HALtheWise/desnat-hopper/Final cut files/Ice chunk.SLDPRT

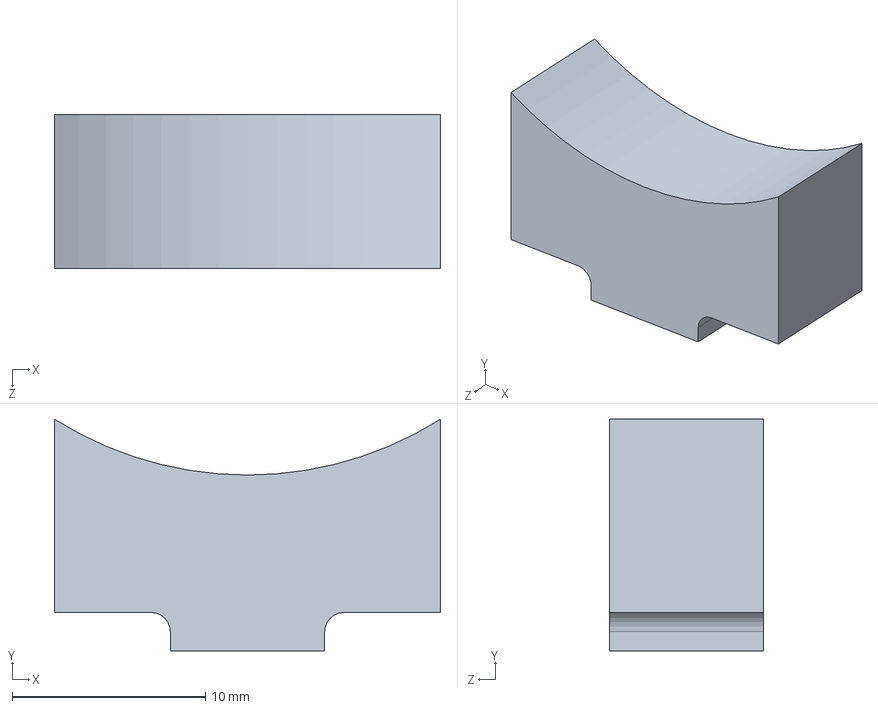
[picture p23: CAD file, 2015-10-23]
Final cut files/Ice chunk.SLDPRT
20.0 x 12.0 x 8.00 mm
