HALtheWise/desnat-hopper/H2 factory/Must be final/Cross tube holder.SLDPRT

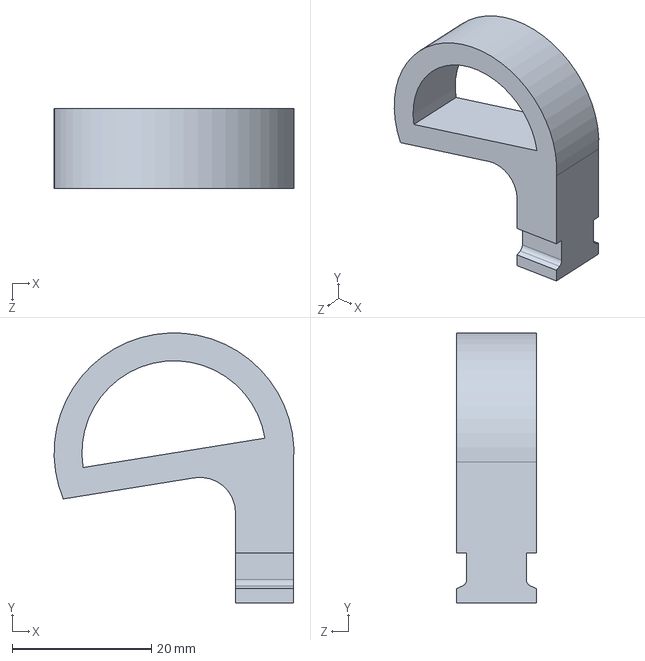
[picture p24: CAD file, 2015-10-20]
H2 factory/Must be final/Cross tube holder.SLDPRT
34.4 x 38.7 x 11.4 mm
