HALtheWise/desnat-hopper/H2 factory/Must be final/printing/Wire holder wide.STL

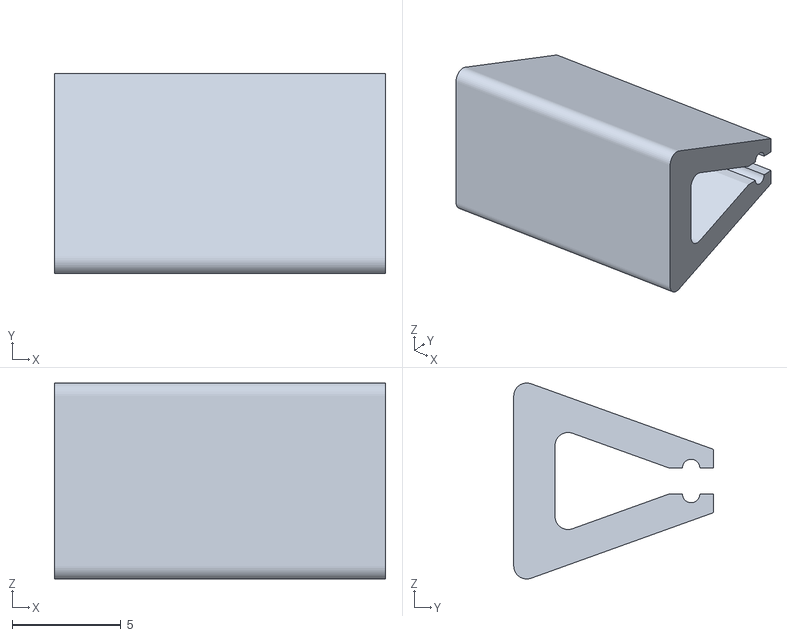
[picture p25: CAD file, 2015-10-19]
H2 factory/Must be final/printing/Wire holder wide.STL
15.2 x 9.19 x 9.02
