HALtheWise/desnat-hopper/H2 factory/Prototype 3/foot.SLDPRT

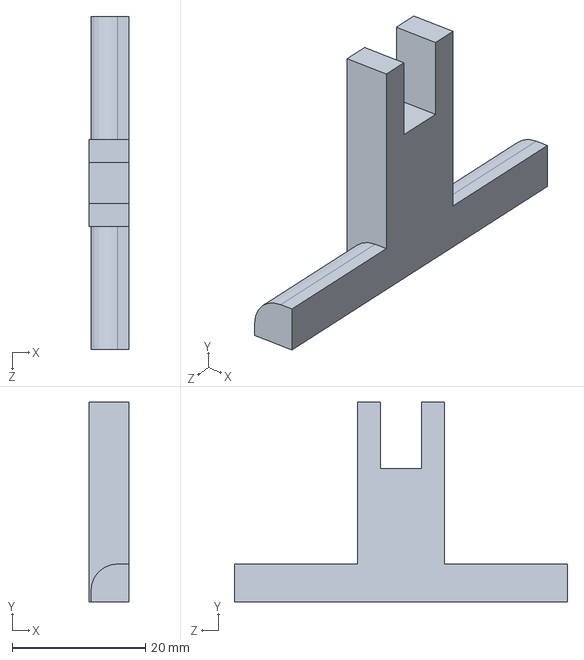
[picture p26: CAD file, 2015-10-12]
H2 factory/Prototype 3/foot.SLDPRT
6.00 x 30.0 x 50.0 mm
