HALtheWise/desnat-hopper/H2 factory/Prototype 3/print files/foot2.STL

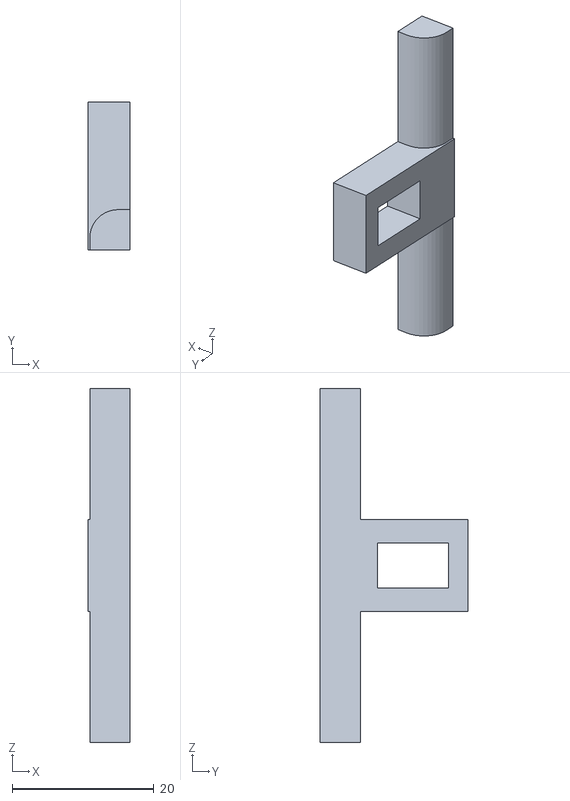
[picture p27: CAD file, 2015-10-12]
H2 factory/Prototype 3/print files/foot2.STL
6.00 x 20.9 x 50.0
