HALtheWise/desnat-hopper/H2 factory/Transport/Hose plug.SLDPRT

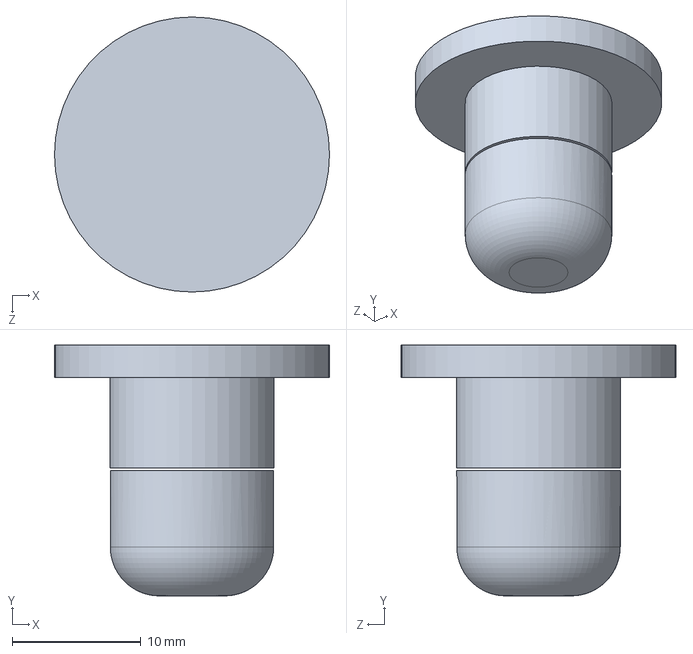
[picture p28: CAD file, 2015-10-15]
H2 factory/Transport/Hose plug.SLDPRT
21.4 x 19.5 x 21.4 mm
