HALtheWise/desnat-hopper/H2 factory/Transport/printing/Hose plug noslice.STL

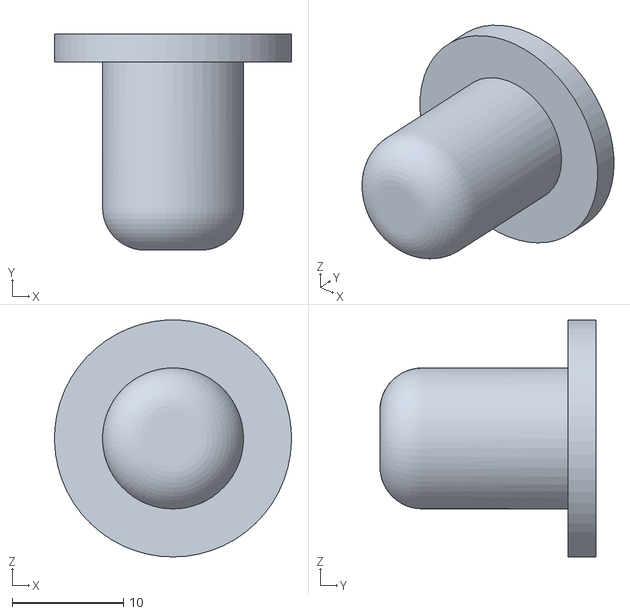
[picture p29: CAD file, 2015-10-15]
H2 factory/Transport/printing/Hose plug noslice.STL
21.4 x 19.5 x 21.3
