HALtheWise/desnat-hopper/Dynamics Simulation/Gondola.SLDPRT

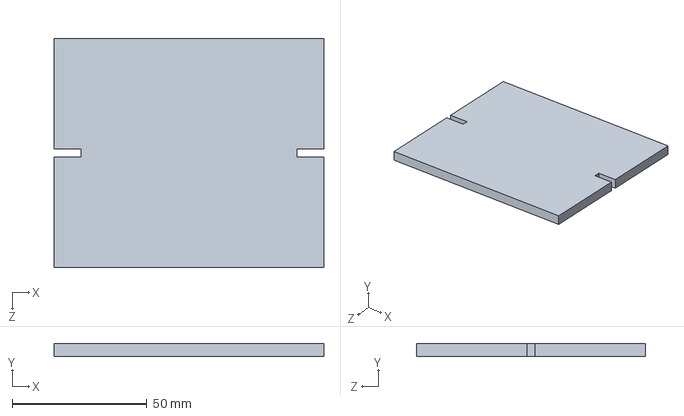
[picture p30: CAD file, 2015-10-03]
Dynamics Simulation/Gondola.SLDPRT
100.0 x 4.76 x 85.0 mm
