HALtheWise/desnat-hopper/Final cut files/Butchered solid part.SLDPRT

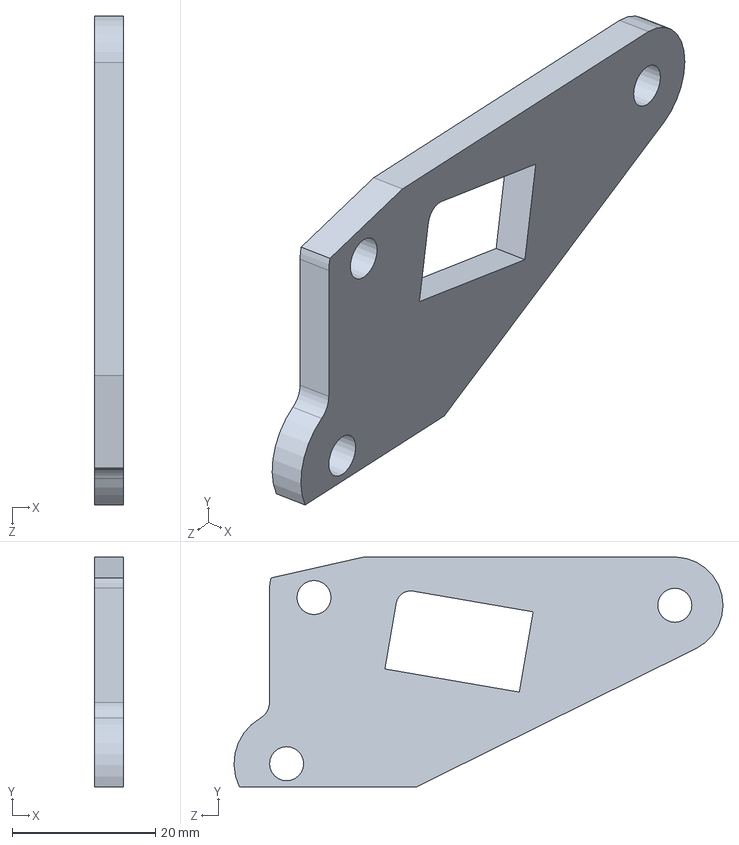
[picture p31: CAD file, 2015-10-23]
Final cut files/Butchered solid part.SLDPRT
4.00 x 32.1 x 68.3 mm
