HALtheWise/desnat-hopper/H2 factory/Must be final/printing/Bubble divider inbetween.STL

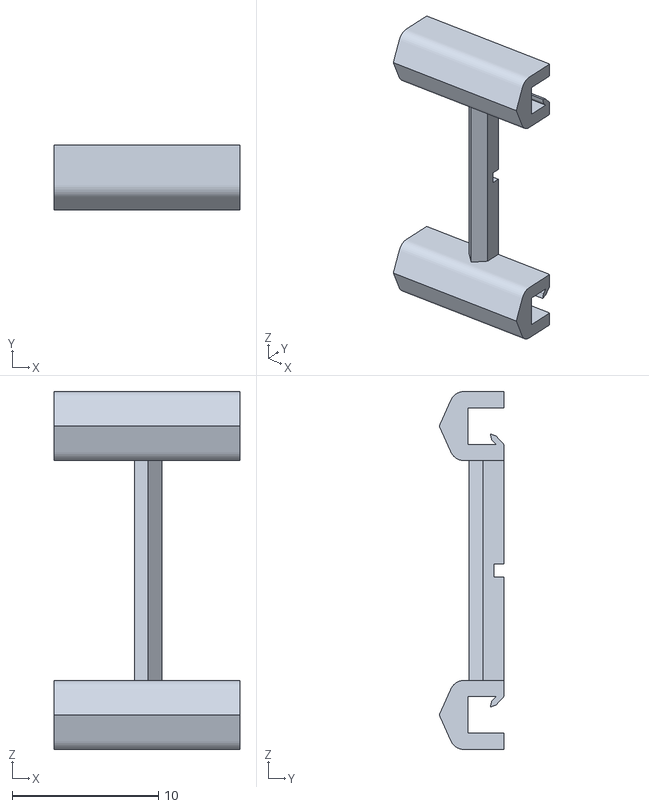
[picture p32: CAD file, 2015-10-19]
H2 factory/Must be final/printing/Bubble divider inbetween.STL
12.7 x 4.42 x 24.5
