HALtheWise/desnat-hopper/H2 factory/Prototype 3/print files/Vertical support center.STL

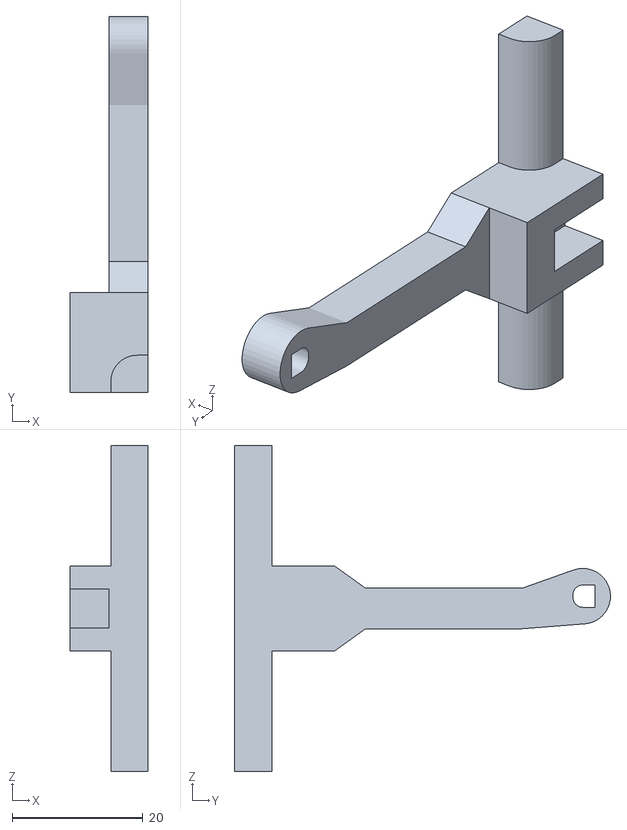
[picture p33: CAD file, 2015-10-12]
H2 factory/Prototype 3/print files/Vertical support center.STL
12.0 x 57.6 x 50.0
