HALtheWise/desnat-hopper/H2 factory/Transport/printing/plug bottompart.STL

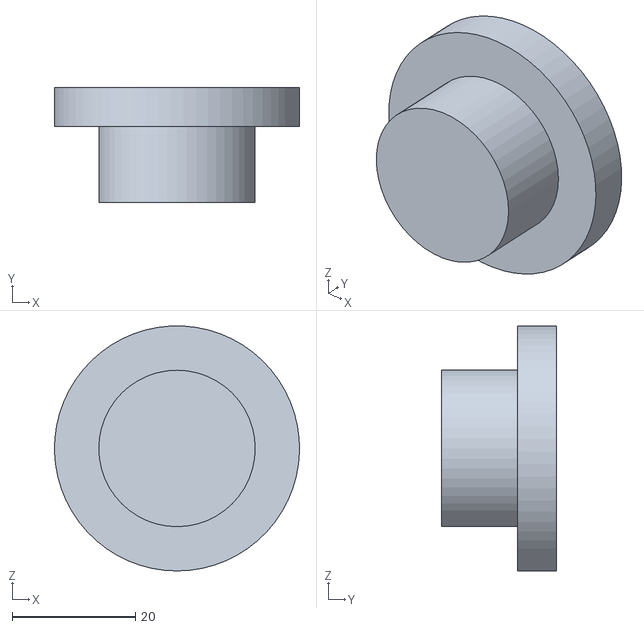
[picture p34: CAD file, 2015-10-15]
H2 factory/Transport/printing/plug bottompart.STL
39.8 x 18.6 x 39.8
