HALtheWise/desnat-hopper/H2 factory/Must be final/printing/Bubble divider 3d.STL

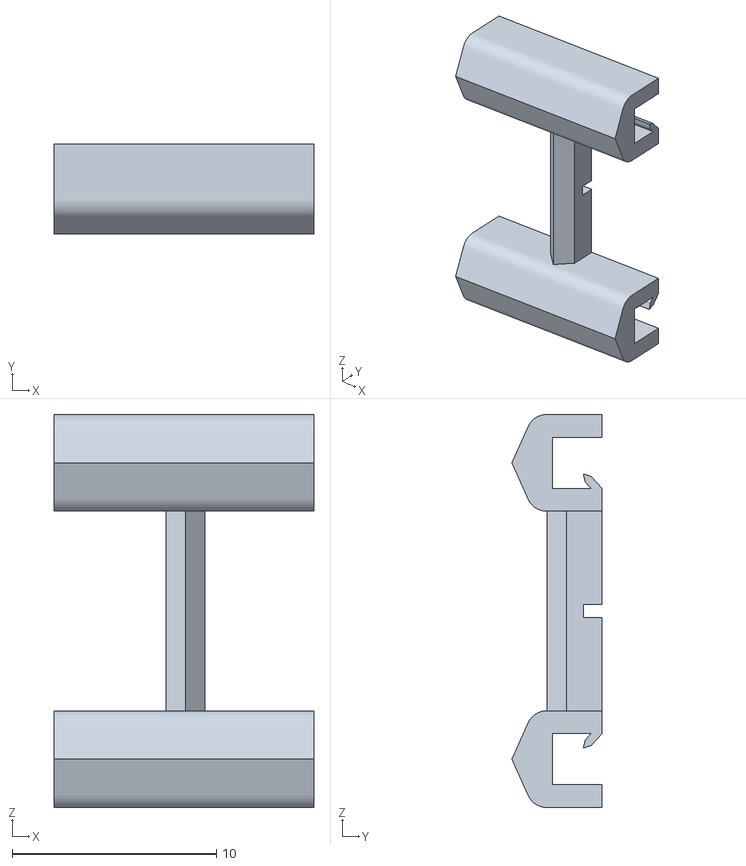
[picture p35: CAD file, 2015-10-19]
H2 factory/Must be final/printing/Bubble divider 3d.STL
12.7 x 4.42 x 19.2
