HALtheWise/desnat-hopper/H2 factory/Must be final/Wire holder.SLDPRT

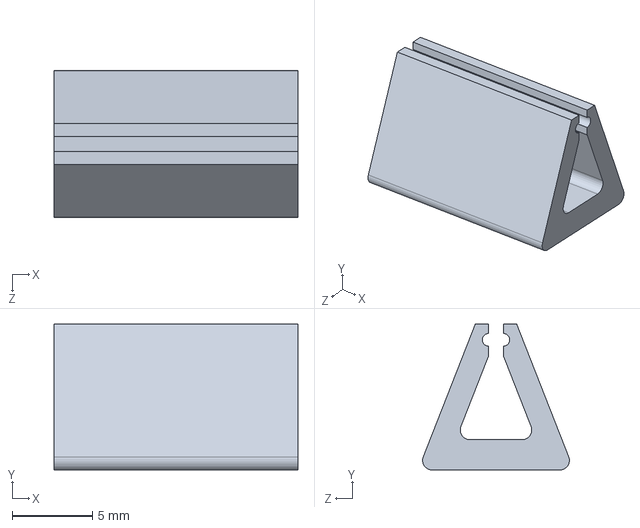
[picture p36: CAD file, 2015-10-19]
H2 factory/Must be final/Wire holder.SLDPRT
15.2 x 9.12 x 9.17 mm
