HALtheWise/desnat-hopper/H2 factory/Transport/printing/plug toppart.STL

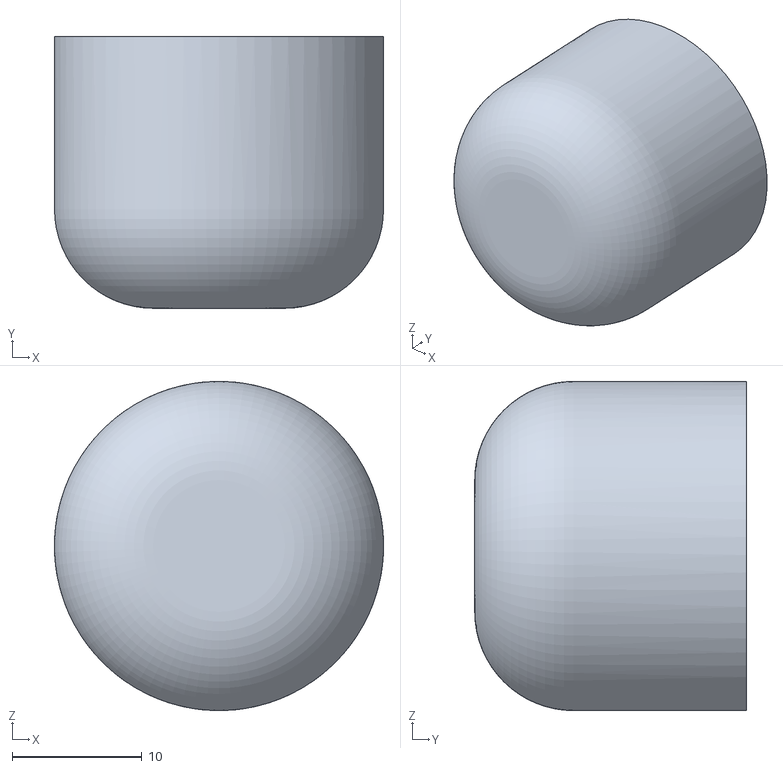
[picture p37: CAD file, 2015-10-15]
H2 factory/Transport/printing/plug toppart.STL
25.4 x 21.0 x 25.4
