HALtheWise/desnat-hopper/H2 factory/Must be final/clip.SLDPRT

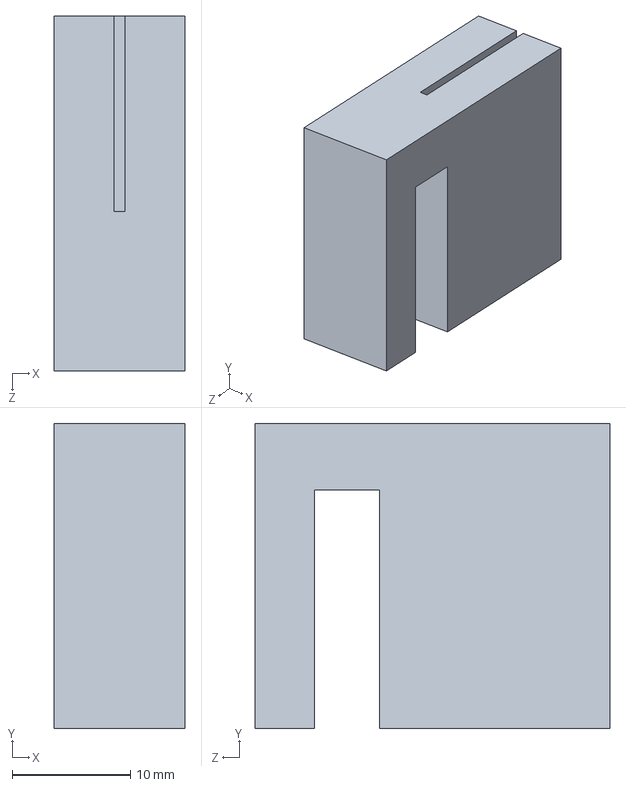
[picture p38: CAD file, 2015-10-19]
H2 factory/Must be final/clip.SLDPRT
11.1 x 25.8 x 30.0 mm
