HALtheWise/desnat-hopper/H2 factory/Prototype 3/Collector.SLDPRT

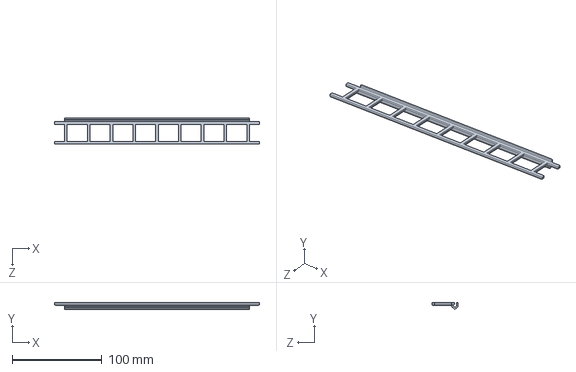
[picture p39: CAD file, 2015-10-12]
H2 factory/Prototype 3/Collector.SLDPRT
228.6 x 7.50 x 29.2 mm
