HALtheWise/desnat-hopper/H2 factory/Prototype 3/print files/foot1.STL

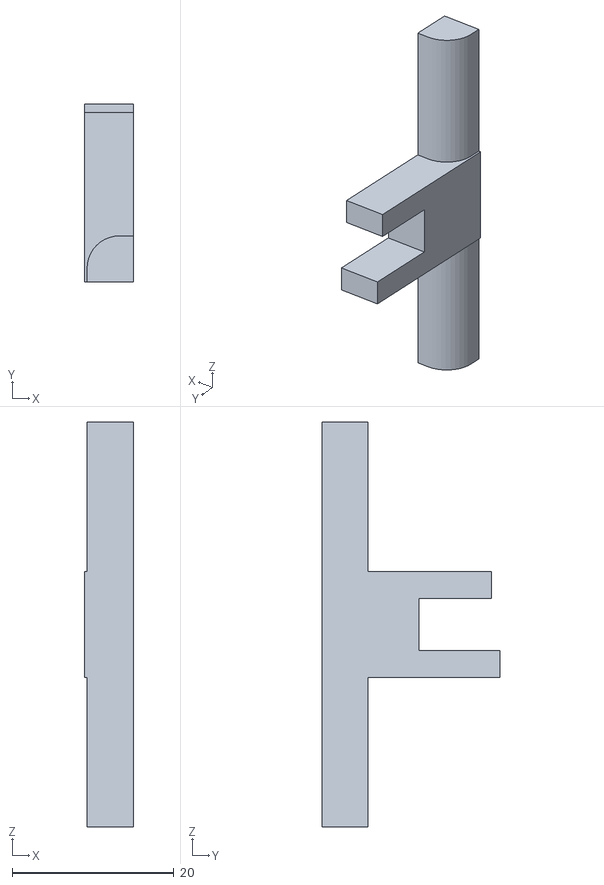
[picture p40: CAD file, 2015-10-12]
H2 factory/Prototype 3/print files/foot1.STL
6.00 x 22.0 x 50.0
