HALtheWise/desnat-hopper/H2 factory/Must be final/metal plate.SLDPRT

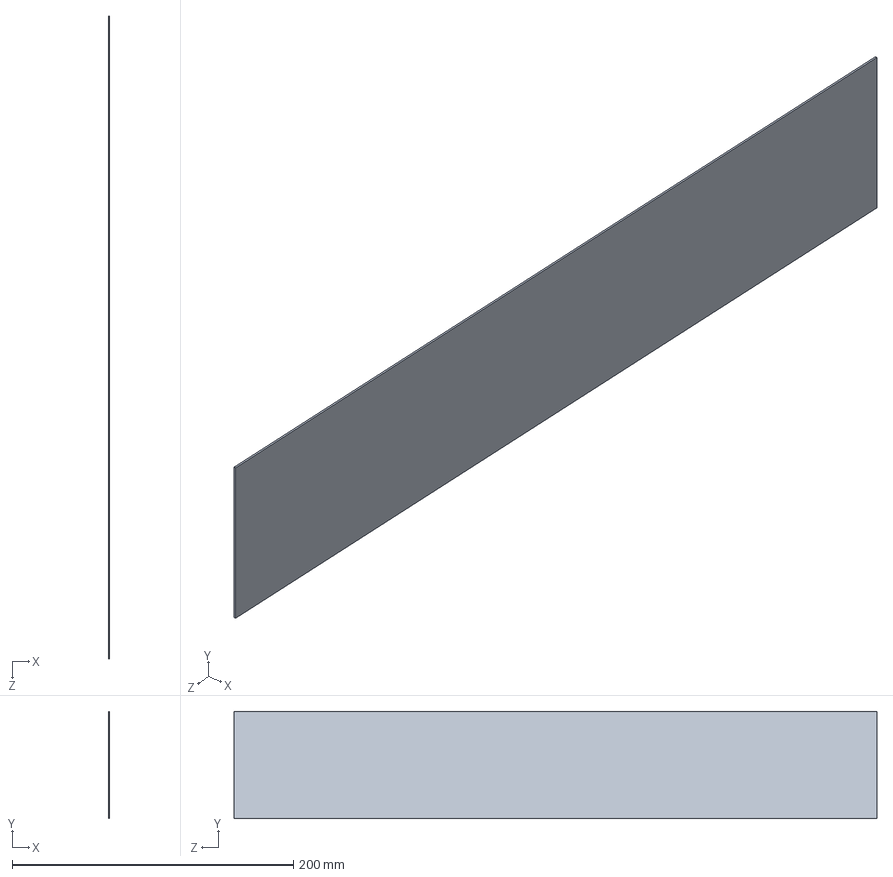
[picture p41: CAD file, 2015-10-19]
H2 factory/Must be final/metal plate.SLDPRT
0.912 x 76.2 x 457.2 mm
