HALtheWise/desnat-hopper/H2 factory/Prototype 3/print files/Vertical support offcenter.STL

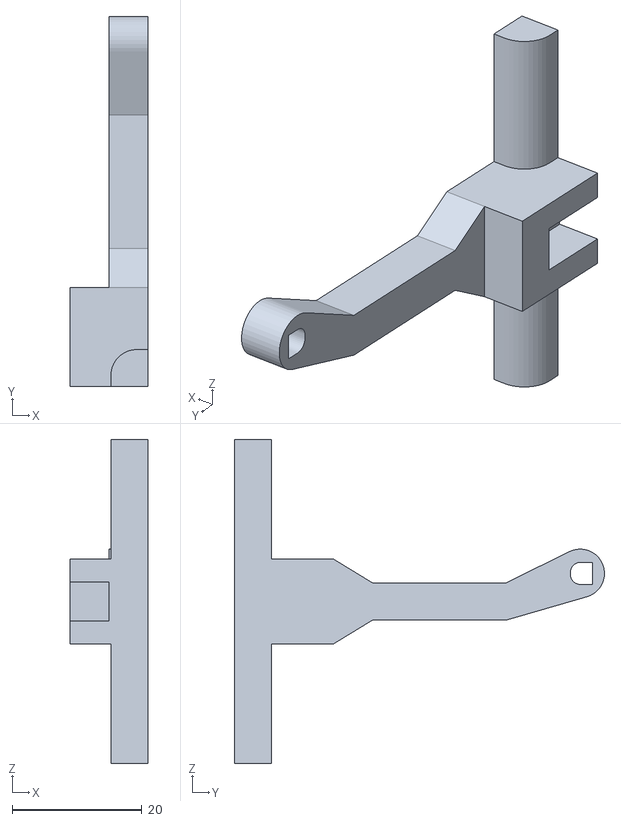
[picture p42: CAD file, 2015-10-12]
H2 factory/Prototype 3/print files/Vertical support offcenter.STL
12.0 x 57.1 x 50.0
