HALtheWise/desnat-hopper/H2 factory/Prototype 3/print files/Electrolyis rig #3.STL

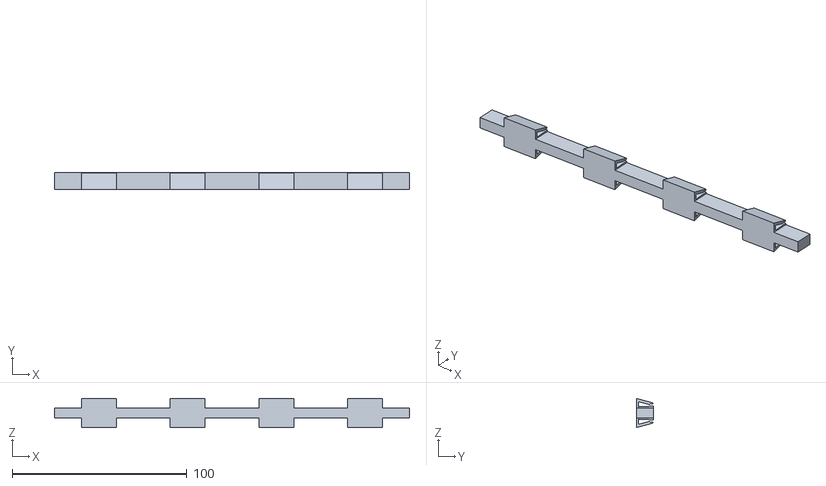
[picture p43: CAD file, 2015-10-12]
H2 factory/Prototype 3/print files/Electrolyis rig #3.STL
203.2 x 9.82 x 16.7
