HALtheWise/desnat-hopper/Final cut files/balloon rebuild.SLDPRT

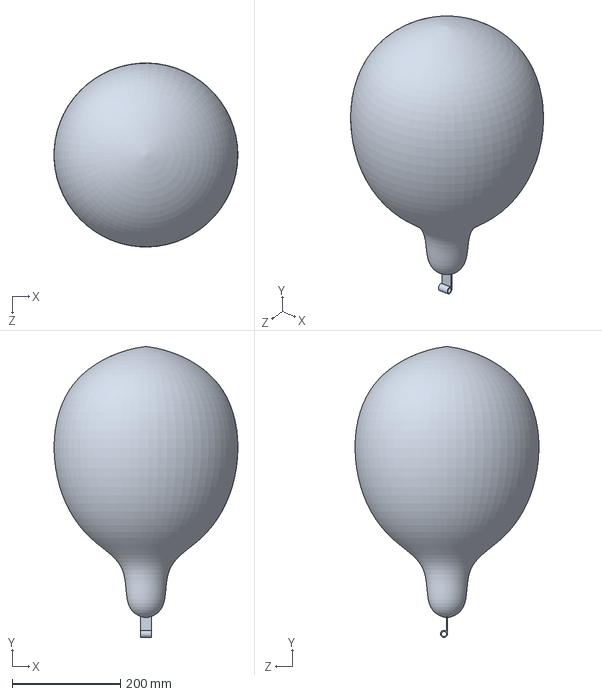
[picture p44: CAD file, 2015-10-14]
Final cut files/balloon rebuild.SLDPRT
340.0 x 538.0 x 340.1 mm
