HALtheWise/desnat-hopper/Final cut files/spring-1986K860.sldprt

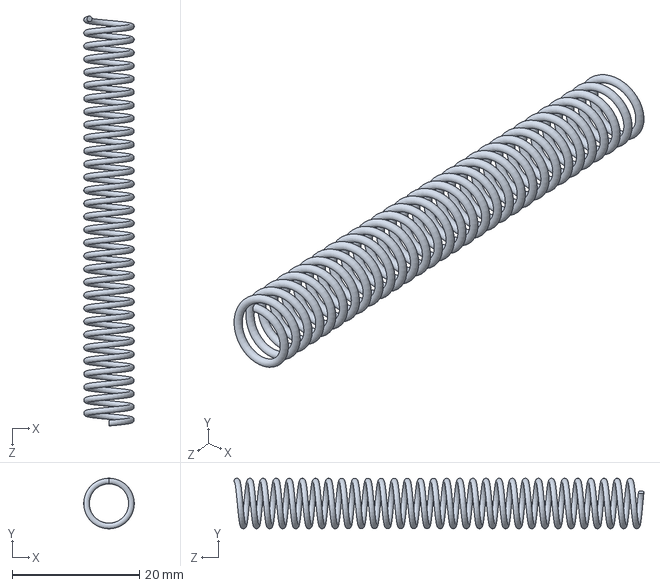
[picture p45: CAD file, 2015-10-14]
Final cut files/spring-1986K860.sldprt
7.95 x 7.95 x 64.4 mm
